A-s-a-d/Table-de-Mixage/DossierPlanification.pdf

BUT 3 – SAE S5 | Dossier organisaonnel
25 décembre 2024 | Version : 2.0 | 1

CY IUT – GEII Neuville

# Dossier organisationnel

## Projet tutoré Mixeur

## Document rédigé par : MUHAMMAD Asad Version : 2.0 [25 décembre 2024]

25 décembre 2024 | Version : 2.0 | 2

## Historique des modifications et révisions de ce document :

N° de version | Date | Auteur | Description et circonstances de la modification
V 0 | | MUHAMMAD Asad | Brouillon : première version, modèle fourni.
V 1.0 | 26/10/2024 | MUHAMMAD Asad | Première rédaction complète du document.
V 1.1 | 26/10/2024 | MUHAMMAD Asad | Modification WBS
V 2.0 | 07/11/2024 | MUHAMMAD Asad | Amélioration basée sur les retours des professeurs et Avancement.

## Avant-propos¹

Le cahier des charges (CDC) du projet est rédigé par le chef de projet. Ce document est élaboré durant la phase d’avant-projet afin de planifier la réalisaon du projet et d’organiser l’équipe de manière efficace.
Bien qu'il puisse aborder des éléments variés allant des moyens de communicaon avec le client aux protocoles de premiers secours en cas d’intervenon chez ce dernier, il doit impéravement inclure les éléments suivants :
- La liste des livrables du projet, regroupés par lots de travaux, présentée sous la forme d’une structure de découpage (SDP), également appelée Work Breakdown Structure (WBS).
- Les jalons du projet, servant de repères essenels pour suivre l'avancement.
- Le planning de réalisaon, souvent illustré sous la forme d’un diagramme de Gan.
Le présent dossier organisaonnel a pour objecf de définir et de clarifier l’organisaon mise en place pour le projet "Table de Mixage". Ce projet doit respecter le cahier des charges rédigé. Le document précise les différentes étapes de développement, la réparon des tâches au sein de l’équipe, ainsi que les modalités de suivi et de contrôle pour garanr la bonne marche du projet.

1
Référence : Geson de projet, 50 ouls pour agir ; F. Bouchaouir, Y. Dennger, O. Englender ; Vuibert ; 2014. L’essenel de la geson de projet ; R. Aïm ; Gualino ; 2022.

25 décembre 2024 | Version : 2.0 | 3

## Table des maères

Avant-propos | 2
Table des maères | 3
Table des Tableaux | 3

1. Planificaon | 4 1.1. Work Breakdown Structure (WBS) | 4 1.2. Jalons | 8 1.3. Planning – Diagramme de Gan | 9 2. Modalités organisaonnelles | 10 2.1. Equipe : | 10 1.1. Rôles des intervenants | 10 1.2. Modalités de maîtrise des livrables techniques | 12 2.2. Modalités de contrôle du travail | 13 3. Clôture du projet | 14

## Table des Tableaux

Tableau 1 Work Breakdown Structure (WBS) | 7
Tableau 2 Jalons | 8
Tableau 3 Membres d'équipe | 10
Tableau 4 Réparon des tâches et des responsabilités | 11
Tableau 5 Documents et Artefacts Finaux | 14

## Table des Figures

Figure 1Diagramme Gan | 9

25 décembre 2024 | Version : 2.0 | 4

## 1. Planificaon

### 1.1. Work Breakdown Structure (WBS)

La WBS pour le projet Table de Mixage est divisée en x grandes pares

2
Cahier des charges

### 3 Document organisaonnelle

4
Dossier de concepon
5
Sous-systèmes
travail Lot de | Tâches | Livrables associés | Responsable du livrables | Personnes ressources
| Rédiger le cahier des charges globales | globale CdC² | Chef de projet | Équipe projet | Équipe pédagogique
| Rédiger le cahier des charges sous systèmes | CdC sous-système | Chaque groupe | Équipe projet | Équipe pédagogique
| Extraire de la liste des livrables | CdC globale | Chef de projet | Équipe projet | Équipe pédagogique
| Réparr le travail dans l’équipe projet | DO³ | Chef de projet | Équipe projet | Chef de projet
| Rédiger le dossier opéraonnel | DO | Chef de projet | Équipe projet | Équipe pédagogique
| Dresser la liste du matériel | Nomenclature | Chef de projet et les groupes | Équipe projet | Équipe
| Dossier de concepon sous-systèmes | sous-système DdC⁴ | Les groupes | Équipe projet | Équipe pédagogique
| Dossier de concepon Globale | DdC globale | Chef de projet | Équipe projet | Équipe pédagogique
| Prototypes des sous-systèmes | Prototypes SS⁵ | Les groupes | Équipe projet | Chef de projet et Équipe pédagogique

Valideur(s) Ges

on de projet

pédagogique Concep

on

25 décembre 2024 | Version : 2.0 | 5

### 6 Document de fabricaon électronique

7

# Procédure et rapport Fabrica

on Document de fabricaon

électronique sous-systèmes et globale | D_fab_elec⁶ | Chef de projet et les groupes | Équipe projet | Chef de projet et Équipe
Rédiger les procédures et rapports de tests des sous-systèmes | P&R⁷de tests des SS | Les groupes | Équipe projet | Équipe pédagogique
Rédiger la procédure et le rapport de maintenance correcve SS | P&R de maintenance correcve | Les groupes | Équipe projet | Équipe pédagogique
Rédiger la procédure et le rapport de maintenance correcve globale | P&R de maintenance correcve | Chef de Projet | Équipe projet | Équipe pédagogique
Effectuer les tests des sous-systèmes | P&R de tests du système | Les groupes | Équipe projet | Chef de projet et Équipe pédagogique
Rédiger la procédure et le rapport de maintenance prévenve SS | P&R de maintenance prévenve | Les groupes | Équipe projet | Équipe pédagogique
Rédiger la procédure et le rapport de maintenance prévenve globale | P&R de maintenance prévenve | Chef de Projet | Équipe projet | Équipe
Rédiger la procédure d’installaon et de mise en service | Procédure d'installaon et de mise en service | Chef de projet et les groupes | Équipe projet | pédagogique Mise en service Équipe
| opéraonnel | Chef de projet et les groupes | Équipe projet | pédagogique Produc Chef de projet et Équipe
Organiser et préparer la soutenance S5 | Soutenance S5 | Chef de projet | Équipe projet | pédagogique Clôture de projet Équipe pédagogique
Organiser et préparer la soutenance S6 | Soutenance S6 | Chef de projet | Équipe projet | Équipe
| exécuté | Chef de projet et les groupes | Équipe projet | Équipe pédagogique

pédagogique Tests et valida

on

on finale Créer un prototype opéraonnel Prototype

pédagogique Livraison finale | Rédiger le dossier d’œuvre exécuté | Dossier d'œuvre

25 décembre 2024 | Version : 2.0 | 6

8
Programme
9
Conversion Numérique Numérique

### 10 Conversaon Analogique Numérique Réalisa

# on du projet / Réparon des tâches Entrées Numériques

Uliser une Raspberry pi 4 | Prog ⁸Raspberry | Asad, Volodymyr | Équipe projet | Chef de projet
Récepon données Midi | | Asad, Volodymyr | Équipe projet | Chef de projet
données MIDI CNN⁹ | | Asad, Volodymyr | Équipe projet | Chef de projet
Gérer le signal sonore synchronisé | | Nathan, Volodymyr | Équipe projet | Chef de projet

Prog Sync
Synchroniser le flux de données | Asad, Volodymyr

Équipe
projet

Chef de
projet Entrées Analogiques
Condionnement des signaux analogiques | SS Condionnement des Signaux Analogique | Asad, Volodymyr | Équipe projet | Chef de projet
CAN¹⁰ données analogiques | | Asad, Volodymyr | Équipe projet | Chef de projet

Prog
Microcontrôleur
Geson des Données CAN | Asad, Volodymyr

Équipe
projet

Chef de
projet
Concepon des Modules et Carte mère | PCB | Asad, Volodymyr | Asad, Volodymyr | Chef de
| | | projet | Chef de
Effets audio Geson de stockage | Prog Raspberry | Nathan, Gabriel | Équipe projet | Chef de projet
Rechercher des soluons pour ampli audio | Liste des composants | Nathan, Gabriel | Équipe projet | Chef de projet
projet IHM | Créer une interface | Prog IHM | Enes, Jibril | Équipe

projet Effets et geson

25 décembre 2024 | Version : 2.0 | 7 Restuon Sonore
Conversaon Numérique Analogique | Prog Raspberry | Nathan, Gabriel | Équipe projet | Chef de projet
Tester des soluons pour l’ampli audio déterminer la soluon finale | Rapport de test | Nathan, Gabriel | Équipe projet | Volodymyr et Chef de projet
Gérer le son en sore des HP | SS Restuon Sonore | Nathan, Gabriel | Équipe
Modéliser la boite pour le prototype | Plans 3D (pièces et assemblage) / Fichiers STL | Benji, Victor | projet Équipe projet | Volodymyr Design Chef de projet
Imprimer la boite | Boite physique | Benji, Victor | Équipe projet | Chef de
Étude de consommaon globale | Document Consommaon Énergéque Système | Benji, Victor | Équipe projet | projet Energie Volodymyr et Chef de projet
Alimentaon Secteur 12V, ±6V | SS Alimentaons Secteur, PCB, | Benji, Victor | Équipe projet | Volodymyr et Chef de projet
Alimentaon Baerie 12V, ±6V | SS Alimentaons Baerie, PCB, | Benji, Victor | | Volodymyr et Chef de
Intégraon des Modules | | Volodymyr, Asad | Équipe projet | projet Intégraon Chef de projet et Volodymyr
Intégrer des sous systèmes | | Volodymyr, Asad | Équipe projet | Chef de projet

Tableau 1 Work Breakdown Structure (WBS)

25 décembre 2024 | Version : 2.0 | 8

### 1.2. Jalons

Jalon | Responsable | Date
Inialisaon du projet | Équipe projet | 05 Oct 2024
Présentaon avant-projet | Client | 24 Oct 2024
Finalisaon des documents d’avant-projet | Équipe projet | 28 Oct2024
Validaon officielle du projet | Client | 10 Nov 2024
Concepon détaillée des modules | Équipe projet | 3 Jan 2025
PCB Modules | Équipe projet | 17 Jan 2025
Test inial des Sous Systèmes | Équipe projet | 21 Jan 2025
Finalisaon et validaon interne prototype alpha | Équipe projet | 5 Mars 2025
Test inial du prototype alpha | Équipe projet | 7 Mars 2025
Livraison du projet final | Équipe projet | 28 Avril au 2 mai 2025

Tableau 2 Jalons

BUT 3 – SAE S5 | Dossier organisaonnel

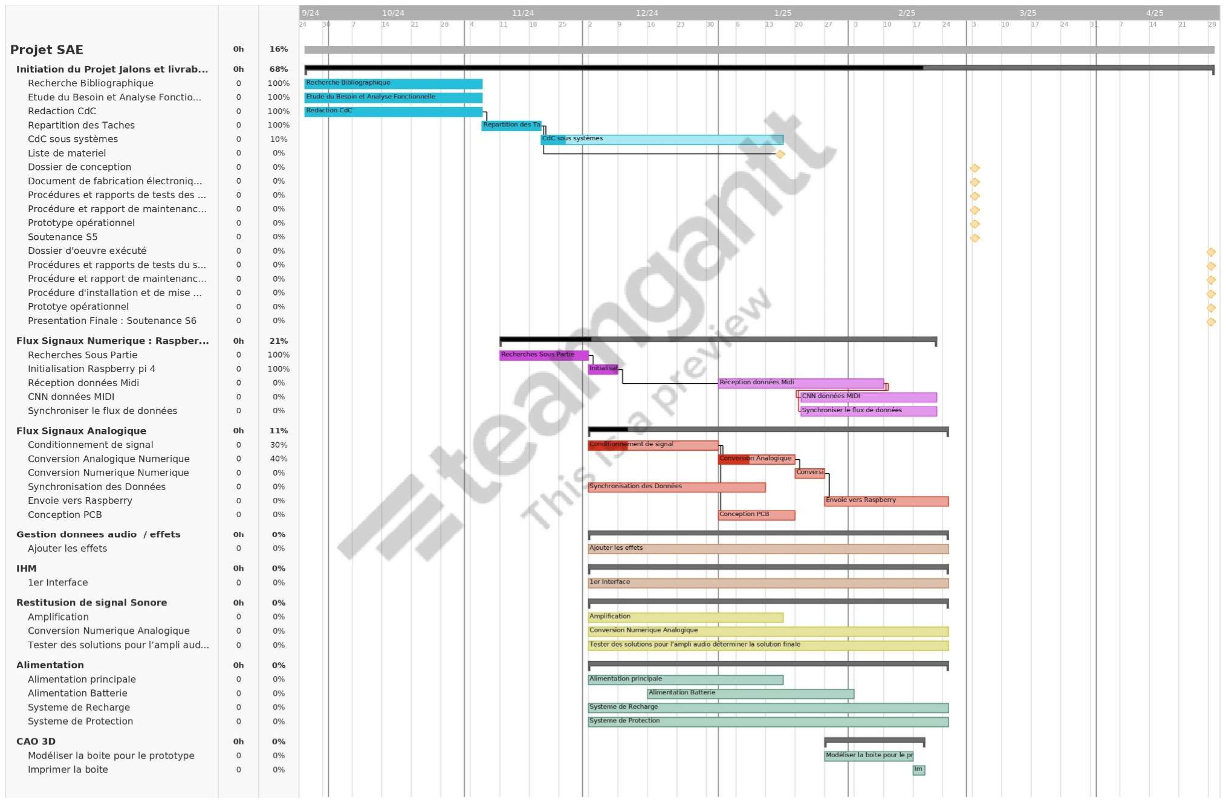
[picture p99: figure]

25 décembre 2024 | Version : 2.0 | 9

### 1.3. Planning – Diagramme de Gan

Les tâches sont répares par personne.

- Bleu – toute l’équipe
- Rouge – Volodymyr & Asad
- Violet: Asad & Volodymyr
- Jaune – Nathan et Gabriel
- Orange – Enes & Djibril.
- Vert –Benjy & Victor

Figure 1Diagramme Gan

25 décembre 2024 | Version : 2.0 | 10

## 2. Modalités organisaonnelles

### 2.1. Equipe :

Nom Prénom
Geson du flux des données | MUHAMMAD Asad
| VRONSKYI Volodymyr
Restuon audio | LATHRO-SERI Nathan
Interface informaque/ physique ulisateur + opéraons sur les signaux | YIGIT Enes

ERBE Gabriel

EL KARANI Djibril
Dimensionnement mécanique/électronique (CAO +
Alimentaon)

RAMIRES MATOS Victor
IDMOND Benjy
Tableau 3 Membres d'équipe

### 1.1. Rôles des intervenants

Chaque membre de l’équipe projet et intervenant extérieur a un rôle défini pour assurer l’avancée du projet.
Rôle | Intervenant (Nom, profil) | Instuon
| Représentaon client
Propriétaire | IUT CY Université | IUT CY Université
Porteur du besoin | ARCINIEGAS Andres | IUT CY Université
Interlocuteur client | GAUTHIER Vincent | IUT CY Université

Équipe projet
Chef de projet | MUHAMMAD Asad | Équipe projet
Responsable de la rédacon du cahier des charges globale | MUHAMMAD Asad | Équipe projet
Responsable de la rédacon du cahier des charges SS | Geson du flux des données | MUHAMMAD Asad | Équipe projet
Restuon audio | LATHRO-SERI Nathan
IHM | YIGIT Enes
CAO + Alimentaon | RAMIRES MATOS Victor
Responsable de la rédacon du document organisaonnel | MUHAMMAD Asad | Équipe projet
Responsables programmaon IHM | YIGIT Enes | Équipe projet
Opéraons sur les signaux | EL KARANI Djibril | Équipe projet
Responsables Sore Audio | LATHRO-SERI Nathan | Équipe projet

25 décembre 2024 | Version : 2.0 | 11
Responsables Amplificaon | ERBE Gabriel | Équipe projet
Responsable modélisaon boier | IDMOND Benjy | Équipe projet
Responsable alimentaon | RAMIRES MATOS Victor | Équipe projet

Intervenants extérieurs
(Technicien, ouvrier,) | Fabien | IUT CY Université

Tableau 4 Réparon des tâches et des responsabilités

25 décembre 2024 | Version : 2.0 | 12

### 1.2. Modalités de maîtrise des livrables techniques

Les livrables techniques seront évaluées selon plusieurs critères détaillés ci-dessous :

### 1. Conception et validation des documents techniques :

o Cahier des charges : Le livrable doit inclure un cahier des charges précis, validant les besoins fonctionnels et les contraintes techniques du projet.
o Plans techniques : La conception des schémas de câblage, des diagrammes de fonctionnement, et des schémas de connexion des composants sera rigoureusement évaluée pour sa clarté et sa précision.
o Simulations des circuits : Avant la réalisation des prototypes, des simulations de circuits seront effectuées (si possible), tant au niveau des modules individuels que du système global, afin de vérifier leur bon fonctionnement sous différentes conditions.

### 2. Validation par tests fonctionnels et de performance :

o Tests sur plaquelab (breadboard) : Les circuits seront testés sur des prototypes montés sur plaque d’essai pour vérifier leur comportement en conditions réelles. Ces tests permettront de valider les performances de chaque module (ex : alimentation, traitement du signal, etc.).
o Tests d’intégration : Une fois les modules validés individuellement, un test d’intégration sera réalisé pour vérifier le bon fonctionnement de sous-système puis système complet, en s’assurant que les interfaces entre les modules et la communication entre les sous-systèmes respectent les exigences.
o Test de programme : Chaque module logiciel sera testé indépendamment (tests unitaires) pour valider ses fonctionnalités avant l’intégration dans le système complet. La validation se fera en vérifiant que chaque fonction du programme respecte les spécifications définies dans le cahier des charges.

### 3. Maintenance et documentation :

o Procédures de maintenance : Des documents seront rédigés pour détailler les procédures de maintenance préventive et corrective. Ces procédures viseront à assurer la longévité du système et à permettre son entretien facile par d’autres intervenants.
o Guides d’utilisation : Des documents détaillant l’utilisation du système final seront rédigés pour faciliter la prise en main par les utilisateurs. Ces guides incluront des instructions sur les réglages, les tests de bon fonctionnement et les éventuelles mises à jour logicielles.

### 4. Suivi de la mise en œuvre et de l’implantation :

o Documentation complète pour l’implantation : Tous les documents nécessaires à l’implantation du système (schémas de câblage, guides d’installation, spécifications des composants) seront fournis, permettant une mise en œuvre fluide et conforme. o Tests de validation finale : Avant la livraison du projet, une série de tests de validation sera réalisée pour garantir que le système final répond aux exigences initiales et fonctionne comme prévu dans un environnement réel d’utilisation.

25 décembre 2024 | Version : 2.0 | 13

### 2.2. Modalités de contrôle du travail

Pour garanr un suivi rigoureux de la qualité et de l'avancement du projet, plusieurs ouls et praques sont mis en œuvre :
Ouls de geson et de versioning :
- Git : Ulisé pour le stockage et la geson des versions du code, des plans, et des documents techniques.
o GitHub (Desktop ou Web) : Un projet GitHub (hps://github.com/A-s-a-d/Table-de-Mixage) a été créé pour centraliser tous les documents nécessaires au projet. Cet oul facilite le suivi des versions et le stockage des fichiers, notamment pour la programmaon.
o GitLab : Une image du projet a été créée sur GitLab, permeant une synchronisaon automaque avec GitHub. GitLab CYU est une plateforme interne de l'université, ulisée pour stocker les documents sur les serveurs de l’établissement. Les éléments du projet doivent obligatoirement être déposés sur l'espace GitLab de l'université. Cependant, l'ulisaon de cet oul nécessite une connexion Internet et une interface Web ce qui n’est pas idéal pour la suivie des modificaons régulièrement. La créaon d'une image de projet basée sur GitHub facilite l'accès et l'ulisaon.
o Git (avec ILC) ou GitKraken (Avec Interface Graphique) : Sur Linux, chaque membre peut choisir d'uliser Git en ligne de commande ou GitKraken pour gérer les modificaons localement. Ces ouls permeent un suivi des versions et des modificaons hors ligne comme GitHub Desktop qui n’est pas disponible sur Linux.
- OneDrive : En complément de GitHub, un dossier OneDrive a été configuré pour faciliter le stockage des documents en cours de rédacon. Ces fichiers sont ensuite sauvegardés et synchronisés sur GitHub pour assurer une centralisaon des données.
o Structure de stockage :
SAE_PROJETTUTORÉ
├───DOCUMENTATION
│ | ├───CDC
│ | ├───PLANIFICATION
│ | ├───PRESENTATION
│ | └───SCHEMAS
└───TECHNIQUE
├───SIGNAL_ANALOGIQUE
│ | ├───ELECTRONICS
│ | │ | ├───SCHEMATICS
│ | │ | ├───SIMULATIONS
│ | │ | └───TESTS
│ | └───PROGRAMMATION
└───SIGNAL_NUMERIQUE
├───ELECTRONICS
└─── PROGRAMMATION
- Cahiers de laboratoire : Chaque membre documente les avancées techniques de ses tâches.
- Réunions hebdomadaires : Revues de l’avancement, obstacles et ajustements éventuels.
- Diagramme de Gan : Suivi des délais et vérificaon des dépendances entre tâches.

25 décembre 2024 | Version : 2.0 | 14

## 3. Clôture du projet

Les documents et artefacts finaux incluent :
- Prototype fonconnel Table de Mixage avec interface et fonconnalités opéraonnelles.
- Documentaon technique complète : Schémas, code source, plans d’implantaon et de maintenance.
- Rapports de tests et validaon : Résultats des tests de fonconnalité, latence, justesse des notes.
Chaque document sera stocké sur GitLab pour le code et les schémas, tandis que les dossiers techniques seront archivés sur le serveur de l’IUT.
Nom du document | Type | Descripon | Lieu de stockage
Cahier des charges | PDF | Précise le contexte, les enjeux, les besoins, définit les objecfs, fonconnalités requises, et contraintes. Ce document constue la référence pour la réalisaon du projet. | GitHub -> GitLab
Document organisaonnel | PDF | Précise les étapes, la réparon des tâches, les rôles, et les modalités nécessaires au déroulement du projet. | GitHub -> GitLab
Diagramme structurel | Image | Illustre l’organisaon interne du système. | GitHub -> GitLab
Diagramme fonconnel | Image | Illustre les foncons du système en forme de diagramme, permet de définir les liens entre différentes foncons et de définir les soluons. | GitHub -> GitLab
Diagramme GANTT | Image | Décrit l’organisaon et la réparon des tâches du projet et permet de planifier le temps nécessaire pour chaque tâche. | GitHub -> GitLab
Cahier de laboratoire | Support physique | Un cahier permeant le suivi de déroulement du projet. Il inclue les notes de chaque séance, tels que les réflexions, les croquis, les tests, les calculs, etc.

Tableau 5 Documents et Artefacts Finaux
