A-s-a-d/Table-de-Mixage/SousSysteme_Entrees/Electronique/CAO_PCB/04-ADC+antiallaising/04-ADC_antialiasing.pdf

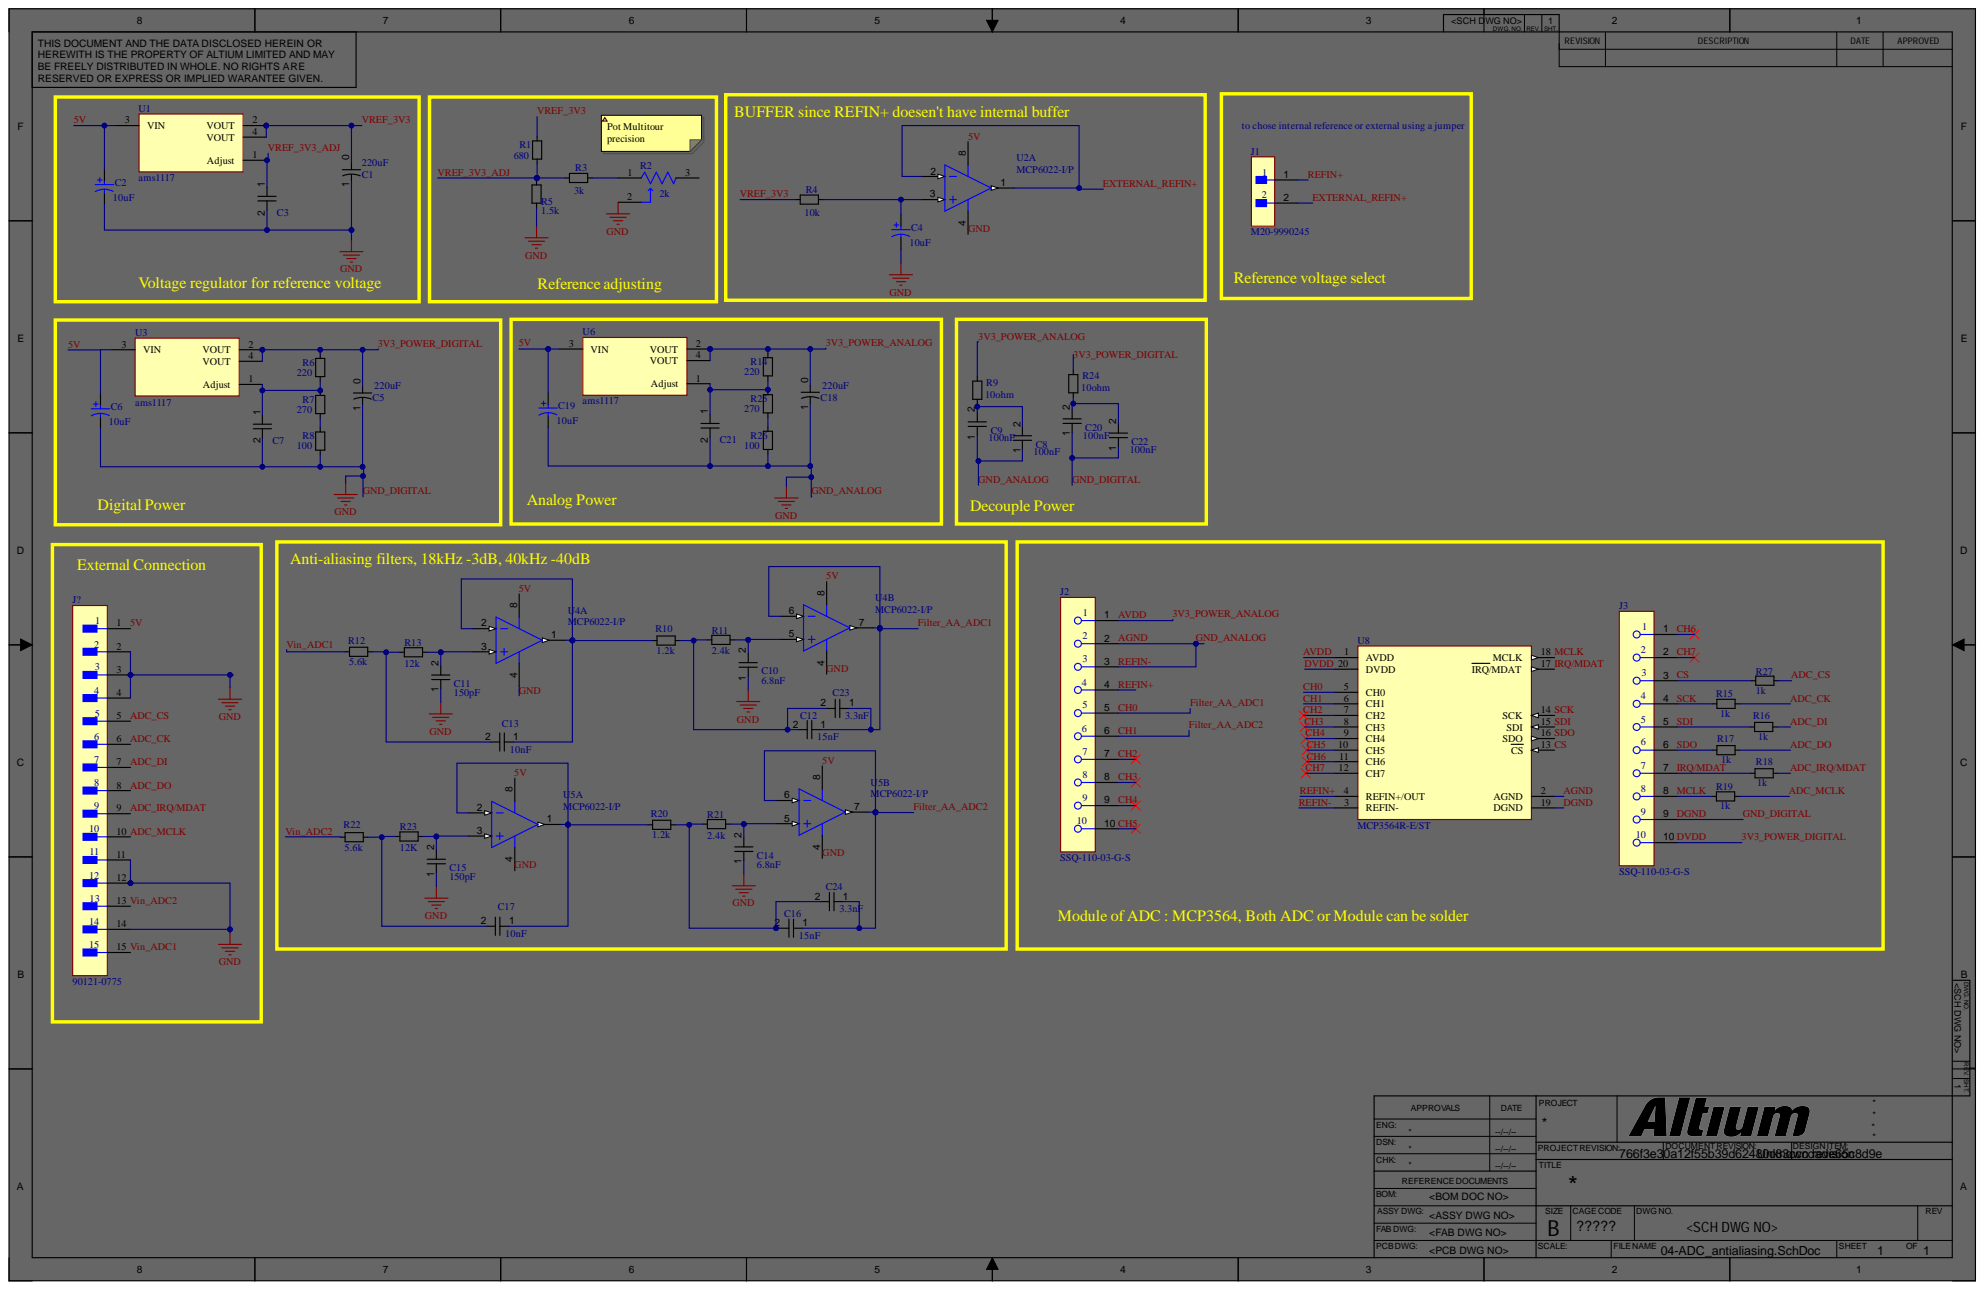
[picture p172: page 1]

DWG. NO. | REV. | SHT. <SCH DWG NO> 1

THIS DOCUMENT AND THE DATA DISCLOSED HEREIN OR HEREWITH IS THE PROPERTY OF ALTIUM LIMITED AND MAY BE FREELY DISTRIBUTED IN WHOLE. NO RIGHTS ARE RESERVED OR EXPRESS OR IMPLIED WARANTEE GIVEN. | | REVISION | DESCRIPTION | DATE | APPROVED

BUFFER since REFIN+ doesen't have internal buffer

to chose internal reference or external using a jumper

Module of ADC : MCP3564, Both ADC or Module can be solder

REV. SHT. DWG. NO.

DATE | PROJECT * | * * APPROVALS * *

ENG: * | --/--/--

DSN: * | --/--/-- | PROJECTREVISION: 766f3e30a12f55b39d6248Un0c8kn3occcd wn raedvisio e65nc8d9e | DOCUMENTREVISION: | DESIGN ITEM:

CHK: * | --/--/--
