A-s-a-d/Table-de-Mixage/SousSysteme_Entrees/Electronique/SIMULATIONS/Circuit_Analog.asc

B: sw; ""
B: sw; ""
C1: cap; 2.2n
C2: cap; 2200n
C3: cap; 4.7µ
D1: diode
L1: ind
R1: res; 3.6172k
R2: res; 3.617k
R3: res; 10Meg
R4: res; 47k
U1: UniversalOpAmp
V1: voltage; AC 1
V2: voltage; SINE(0 1 120)
VCC: voltage; 6
VDD: voltage; -6
Named nets: 0, IN1, VCC, VPP, Vout, IN1_1, Vout_1
.ac oct 500 20 50k
.tran .1
Adaptation du 
Signal si Besoins
AMPLI
Relais
1
2
ON = 1
OFF = 2
Relais
1
2
ON = 1
OFF = 2
2
1
2
1
B
B
