A-s-a-d/Table-de-Mixage/SousSysteme_Entrees/Electronique/SIMULATIONS/Clock clamping.asc

D1: zener; BZX85C3V3
R1: res; 10
V1: voltage; PULSE(0 9 0 0n 0n 25n 50n)
Named nets: 0
.model BZX85C3V3 D ( IS=5n RS=5m BV=3.3 IBV=5m N=1.2 Cjo=200p Vj=0.75 M=0.33 TT=10n )
.tran 200n
