A-s-a-d/Table-de-Mixage/SousSysteme_Entrees/Electronique/SIMULATIONS/Detection_de_Niveau__Adaptation_de_Niveau.asc

C3: cap; 4.7µ
D1: diode
R4: res; 47k
VCC: voltage; 6
VDD: voltage; -6
Named nets: 0, VCC, VPP, V_BP_Filter, V_peak, V_CTRL_Relais
.ac oct 500 20 50k
.tran .1
Adaptation du 
Signal si Besoins
V_BP_Filter = Sortie de filtre passe bas
