A-s-a-d/Table-de-Mixage/SousSysteme_Entrees/Electronique/SIMULATIONS/Filtre_passe_bande.asc

C1: cap; 2.2n
C2: cap; 2200n
R1: res; 3.6172k
R2: res; 3.617k
R3: res; 10Meg
U1: UniversalOpAmp
V1: voltage; SINE(0 1 1000)
VCC: voltage; 6
VDD: voltage; -6
Named nets: 0, IN1, VCC, VPP, V_BP_Filter
.ac oct 500 1 30k
.tran .1
