A-s-a-d/Table-de-Mixage/SousSysteme_Entrees/Electronique/SIMULATIONS/Indicateur_Niveau.asc

D1: LED
R1: res; 330
V1: voltage; 3
Named nets: 0
.tran .1
