A-s-a-d/Table-de-Mixage/SousSysteme_Entrees/Electronique/SIMULATIONS/MIDI_opto.asc

D1: diode
Q1: npn; 2N2222
Q2: npn; 2N2222
R1: res; 220
R2: res; 820
R3: res; 220
R4: res; 1
R5: res; 100k
R6: res; 100k
R7: res; 1k
R8: res; 1k
R9: res; 1k
R10: res; 1k
U1: 4N25
U2: 4N25
V1: voltage; PULSE(0 3.3 0 0 0 5u 10u)
V2: voltage; 3.3
Named nets: 0, Sig_MIDI, Vcc, Sig_out_midi, Sig_Mid_outi_fast
.tran 40u
