A-s-a-d/Table-de-Mixage/SousSysteme_Entrees/Electronique/SIMULATIONS/Offset.asc

C2: cap; 100nF
R2: res; 390
R3: res; 130
R5: res; 1k
R6: res; 1k
U2: UniversalOpAmp2
V1: voltage; 3.3
V3: voltage; SINE(0 1.65 5)
VCC: voltage; 3.3V
Named nets: 0, 3V3, 825mV, VCC, V_Offset_In, V_offset_out
.tran 1
