A-s-a-d/Table-de-Mixage/SousSysteme_Entrees/Electronique/SIMULATIONS/Peak_detector.asc

C1: cap; 10µ
D1: diode
D2: diode
D3: LED
Q1: npn; 2N2222
R1: res; 22k
R2: res; 10k
R3: res; 22k
R4: res; 22k
R5: res; 2k2
R6: res; 2k2
U1: UniversalOpAmp2
U3: UniversalOpAmp2
V1: voltage; 12
V2: voltage; -12
Vin: voltage; SINE(0 5 100)
Named nets: 0, V+, V-
.tran .1
