A-s-a-d/Table-de-Mixage/SousSysteme_Entrees/Electronique/SIMULATIONS/Protection_surtensions.asc

D1: TVSdiode; TVS1
D2: zener; BZX85C3V3
D3: zener; BZX85C3V3
R1: res; 1k
R2: res; 100k
R3: res; 1k
R4: res; 100k
V1: voltage; SINE(0 10 1e6 0 100k)
Named nets: 0, Vin, V_out_TV2, Vout_2*Zener
.tran 20u
.model TVS1 D(Ron=.65 Roff=50Meg Vfwd=3.3 epsilon=6 Vrev=3.3 revepsilon=6 Vpk=24 mfg=Littlefuse type=TVS)
.model BZX85C3V3 D ( IS=5n RS=5m BV=3.3 IBV=5m N=1.2 Cjo=200p Vj=0.75 M=0.33 TT=10n )
