A-s-a-d/Table-de-Mixage/SousSysteme_Entrees/Electronique/SIMULATIONS/Schema_avec_modules.asc

B: sw; ""
B: sw; ""
C1: cap; 2.2n
C2: cap; 2200n
C3: cap; 4.7µ
D1: diode
L1: ind
R1: res; 3.6172k
R2: res; 3.617k
R3: res; 10Meg
R4: res; 47k
U1: UniversalOpAmp
V1: voltage; SINE(0 1 120)
V2: voltage; SINE(0 1 120)
VCC: voltage; 6
VDD: voltage; -6
Named nets: 0, VCC, VPP, V_BP_Filter_1, IN1, V_peak, IN2, V_Peak_Adapté, V_CTRL_Relais_1, V_IN_AMP_1, V_OUT_AMP_1, V_OUT_Relais_1
Adaptation du 
Signal si Besoins
Module : AMPLI
Relais
1
2
ON = 1
OFF = 2
Relais
1
2
ON = 1
OFF = 2
2
1
2
1
B
B
Carte_Mere
Bornier Alimentation 
+ entrees et Sortie
+ connecteurs pour des modules
Module : Filtre passe bas
Module : Detection de Niveau 
+ Adaptation de Niveau
Circuit_relais
Protection
Module : Selection_Voie
x2 pour chaque entrée
STM32 Nucleo L432kc
Analog IN
I/O autre si besoin
OUT_TO_Raspberry
D'autres Composants : 
- Ecran ?
- BP
- LEDs
SYNC
Indicateur niveau
Mixeur
