A-s-a-d/Table-de-Mixage/SousSysteme_Entrees/Electronique/SIMULATIONS/Selection_voie.asc

B: sw; ""
B: sw; ""
L1: ind
VCC: voltage; 6
VDD: voltage; -6
Named nets: 0, VCC, VPP, V_BP_Filter, V_CTRL_Relais, V_OUT_Relais
AMPLI
Relais
1
2
ON = 1
OFF = 2
Relais
1
2
ON = 1
OFF = 2
2
1
2
1
B
B
V_CTRL_Relais = controle relais
V_BP_Filter = sortie de Filtre passe bande
Circuit_relais
Protection
Opto + Transistor + ...
