A-s-a-d/Table-de-Mixage/SousSysteme_Entrees/Electronique/SIMULATIONS/STM32 power.asc

12V: voltage; 12
C1: polcap; 10µ; V=16 Irms=540m Rser=0.24 Lser=4.5n
C2: cap; 10n
C3: polcap; 100µ
D1: schottky; 1N5819
load_or_microcontrollers_power_consumption: load; PULSE(10m 1000m 0 2 2 0 2 3)
R1: res; 510; tol=0
R2: res; 2345; tol=0
R20: res; 1; tol=0
U2: LT1117
Named nets: 0
.tran 2
For simulation
3.3V
Vout = 1.25 * (1+(R2+R20/R1)
