A-s-a-d/Table-de-Mixage/SousSysteme_Entrees/Electronique/SIMULATIONS/Suiveur.asc

6V: voltage; 6
-6V: voltage; -6
U1: UniversalOpAmp
V3: voltage; ""; AC 1
Named nets: 0, V_audio
.ac oct 500 1 20k
