A-s-a-d/Table-de-Mixage/SousSysteme_Entrees/Electronique/SIMULATIONS/Variable-3V3 source for Offset_5k.asc

12V: voltage; SINE(12 1 50)
C1: polcap; 10µF; V=16 Irms=540m Rser=0.24 Lser=4.5n
C2: cap; 10n
C3: polcap; 220µ
D1: schottky; 1N5819
load_or_microcontrollers_power_consumption: load; PULSE(10m 1000m 0 2 2 0 2 3)
R1: res; 750
R2: res; {R}
R3: res; 2.2k
R5: res; 1.5k
R51: res; 300
U2: LT1117
Named nets: 0
For simulation
3.3V
.step param R 1 5000 100
.op
