A-s-a-d/Table-de-Mixage/SousSysteme_Entrees/Electronique/SIMULATIONS/Voltage clamping.asc

D1: zener; BZX85C3V3
R2: res; 220
U1: UniversalOpAmp2
V1: voltage; SINE(2.5 2.5 300 0 50)
V2: voltage; 3.3V
Named nets: Vin, 0, Vcc, Vout_Clamp_zener, Vout_clamp_opamp
.tran 0 0.1 0 1u
https://electronics.stackexchange.com/questions/660780/how-can-i-clip-a-voltage-upper-limit-in-an-analog-signal
.model BZX85C3V3 D ( IS=5n RS=5m BV=3.3 IBV=5m N=1.2 Cjo=200p Vj=0.75 M=0.33 TT=10n )
