A-s-a-d/Table-de-Mixage/SousSysteme_Entrees/Linux_WorkSpace/C_Cpp_Programming/Exemples/Uart_data/src/main.cpp

/*
 * serialTest.c:
 *	Very simple program to test the serial port. Expects
 *	the port to be looped back to itself
 *
 * Copyright (c) 2012-2013 Gordon Henderson.
 ***********************************************************************
 * This file is part of wiringPi:
 *      https://github.com/WiringPi/WiringPi
 *
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
 *    You should have received a copy of the GNU Lesser General Public License
 *    along with wiringPi.  If not, see <http://www.gnu.org/licenses/>.
 ***********************************************************************
 */

#include "Proj_external_lib.h"
int main()
{
    int fd;
    int count;
    unsigned int nextTime;

    if ((fd = serialOpen("/dev/ttyAMA0", 115200)) < 0)
    {
        fprintf(stderr, "Unable to open serial device: %s\n", strerror(errno));
        return 1;
    }

    if (wiringPiSetup() == -1)
    {
        fprintf(stdout, "Unable to start wiringPi: %s\n", strerror(errno));
        return 1;
    }

    nextTime = millis() + 300;
    while (1)
    {
        /* code */

        for (count = 0; count < 256;)
        {
            if (millis() > nextTime)
            {
                printf("\nOut: %3d: ", count);
                fflush(stdout);
                serialPutchar(fd, count);
                nextTime += 300;
                ++count;
            }

            delay(1);

            /*    while (serialDataAvail(fd))
               {
                   printf(" -> %3d", serialGetchar(fd));
                   fflush(stdout);
               } */
        }
    }
    serialClose(fd);
    printf("\n");
    return 0;
}
